remov-b4-flight/LrTMAX/Core/Src/led.c

/**
 *	@file		led.c
 *	@brief		(WS2812B style) RGB LEDs control functions
 *	@author		remov-b4-flight
 *	@copyright	3-Clause BSD License
*/

#include <string.h>
#include "main.h"
#include "LrCommon.h"
#include "led.h"

extern TIM_HandleTypeDef htim3;
extern TIM_HandleTypeDef htim14;
extern bool	isLEDsendpulse;
extern uint8_t	LED_Scene[SCENE_COUNT][LED_COUNT];

uint8_t	LEDColor[LED_COUNT];		// coded LED color value
uint16_t	LEDPulse[TOTAL_BITS+1];	// Data formed PWM width send to LED
uint8_t	LEDTimer[LED_COUNT];		// Individual LED Timer Counter

/**
 * @brief RGB LED intensity table
 * @details define Light intensity for each R,G,B
 * values forms array indexed by LED_XXX (in enum led_color_t)
 */
const LEDDATA LEDTable[COLOR_MAX] = {
	//			R		G		B
	{.rgbw = {.r=LOFF,.g=LOFF,.b=LOFF}},//LED_OFF,
	{.rgbw = {.r=LMAX,.g=LOFF,.b=LOFF}},//LED_RED,
	{.rgbw = {.r=LOFF,.g=LOFF,.b=LMAX}},//LED_BLUE,
	{.rgbw = {.r=LOFF,.g=LMAX,.b=LOFF}},//LED_GREEN,
	{.rgbw = {.r=LMAX,.g=LMAX,.b=LMAX}},//LED_WHITE,
	{.rgbw = {.r=LHLF,.g=LHLF,.b=LOFF}},//LED_YELLOW,
	{.rgbw = {.r=LHLF,.g=LOFF,.b=LHLF}},//LED_MAGENTA,
	{.rgbw = {.r=LOFF,.g=LHLF,.b=LHLF}},//LED_CYAN,
	{.rgbw = {.r=LMAX,.g=LQTR,.b=LOFF}},//LED_ORANGE,
	{.rgbw = {.r=LQTR,.g=LQTR,.b=LQTR}},//LED_GLAY,
	{.rgbw = {.r=LDRK,.g=LDRK,.b=LDRK}},//LED_DARK,
	{.rgbw = {.r=LHIL,.g=LHIL,.b=LHIL}},//LED_HILIGHT,
	{.rgbw = {.r=LMAX,.g=LQTR,.b=LHLF}},//LED_PINK,
	{.rgbw = {.r=LQTR,.g=LMAX,.b=LQTR}},//LED_MINT,
	{.rgbw = {.r=LHLF,.g=LOFF,.b=LOFF}},//LED_DARKRED,
	{.rgbw = {.r=LOFF,.g=LHLF,.b=LOFF}},//LED_DARKGREEN,
	{.rgbw = {.r=LOFF,.g=LOFF,.b=LHLF}},//LED_DARKBLUE,
	{.rgbw = {.r=LHLF,.g=LDRK,.b=LOFF}},//LED_DARKORANGE,
	{.rgbw = {.r=LDRK,.g=LDRK,.b=LOFF}},//LED_DARKYELLOW,
	{.rgbw = {.r=LOFF,.g=LDRK,.b=LDRK}},//LED_DARKCYAN,
	{.rgbw = {.r=LDRK,.g=LOFF,.b=LDRK}},//LED_DARKMAGENTA,
};
/**
 * @brief Test pattern data when on offline
 */
const uint8_t LED_Testpattern[LED_COUNT] = {
	LED_WHITE,LED_RED,LED_ORANGE,LED_YELLOW,
	LED_GREEN,LED_CYAN,LED_BLUE,LED_MAGENTA,
};
/**
 * @brief	LED Initialize - Sets all LEDs to 'OFF'
 * @pre		TIM3 Initialized.
 */
void LED_Initialize() {
	memset(LEDColor, LED_OFF, LED_COUNT);
	memset(LEDTimer, LED_TIMER_CONSTANT, LED_COUNT);
	LED_SendPulse();
}

/**
 * @brief Delay process in us unit.
 * @note Delay period defined as TIM_PERIOD_NPIX
 */
static void LED_Delay_us() {
	HAL_TIM_Base_Start(&htim14);
	htim14.Instance->SR = 0;

	while((htim14.Instance->SR & TIM_SR_UIF) == 0)	;	//wait until timer up.

	HAL_TIM_Base_Stop(&htim14);
}

/**
 * @brief alter LED contents by scene
 * @param scene	Scene No
 */
void LED_SetScene(uint8_t scene) {
	memcpy(LEDColor, LED_Scene[scene], LED_COUNT);
	LED_SendPulse();
}

/**
 *	@brief	Sets decorative color pattern to LEDs.
 */
void LED_TestPattern() {
	memcpy(LEDColor, LED_Testpattern, LED_COUNT);
	LED_SendPulse();
}

/**
 *	@brief	Make LED flashing by setting LEDTimer[]
 *	@param	index	index of LEDs.
 *	@param	color	color of LED.
 *	@param	pulse	duration of pulse in 24ms unit(i.e. pulse=25 => 600ms).
 */
inline void LED_SetPulse(uint8_t index, uint8_t color, uint8_t pulse) {
	LEDColor[index] = color;
	LEDTimer[index] = pulse;
	isLEDsendpulse = true;
}

/**
 *	@brief	make LEDPulse[] from LEDColor[]
 *	@pre	LEDColor[] contains LED color setting.
 */
static void Color2Pulse() {
	uint8_t	pulse = 0;
	LEDDATA	leddata;
	//Convert LEDColor[] to LEDPulse[];
	for(uint8_t led = 0; led < LED_COUNT; led++){
		uint8_t c = LEDColor[led];
		leddata.n = LEDTable[c].n;
		for (uint32_t mask = B31_MASK; mask > B7_MASK; mask >>= 1){
			LEDPulse[pulse++] = (leddata.n & mask)? PWM_HI:PWM_LO;
		}
	}
	//Set 'RESET' state when PWM completed.
	LEDPulse[TOTAL_BITS] = 0;
}

/**
 *	@brief	Send PWM pulses to LEDs rely on LEDColor[] array
 *	@pre	LEDPulse[] contains pulse width array.
 *	@return	result of Send
 */
bool LED_SendPulse() {

	bool r = true;
	//Convert LEDColor[] to LEDPulse[]
	Color2Pulse();

	//Send 'RESET' signal(280us > low data) for LEDs
	GPIOA->ODR |= GPIO_PIN_6;	//'RESET' state
	//Set PA6 AF -> GPIO
	GPIOA->MODER &= ~(GPIO_MODER_MODER6_1);
	GPIOA->MODER |=	GPIO_MODER_MODER6_0;
	//Earning 'RESET' Time period.
	LED_Delay_us(LED_RESET_WIDTH);
	//Set PA6 GPIO -> AF
	GPIOA->MODER ^= (GPIO_MODER_MODER6_1|GPIO_MODER_MODER6_0);
	htim3.Instance->CNT = (PWM_PERIOD);

	//Start DMA
	if (HAL_TIM_PWM_Start_DMA(&htim3, TIM_CHANNEL_1, (uint32_t *)LEDPulse, TOTAL_BITS + 1) != HAL_OK) {
		r = false;
	}
	return r;
}

/* ******************************************************* **** END OF FILE****/
