remov-b4-flight/LrTMAX/Core/Inc/key_define.h

#ifndef _USB_HID_H
#define _USB_HID_H

/**
 * @brief key definition structure.
 */
typedef struct enc_sw_define_t {
	uint8_t	axis;
	uint8_t color;
	uint8_t period;
} ENC_SW_DEFINE;

#define RIGHTA	"\x7b"
#define LEFTA	"\x7c"
#define UPA		"\x7d"
#define DOWNA	"\x7e"

#define MASK_ENC_SW		0x0000ffff
#define MASK_ENC		0xffff0000
#define MASK_ENCPUSH	0x0000ff00

#endif /*_USB_HID_H */
